chem64/RECU/readme/RECU_1.png

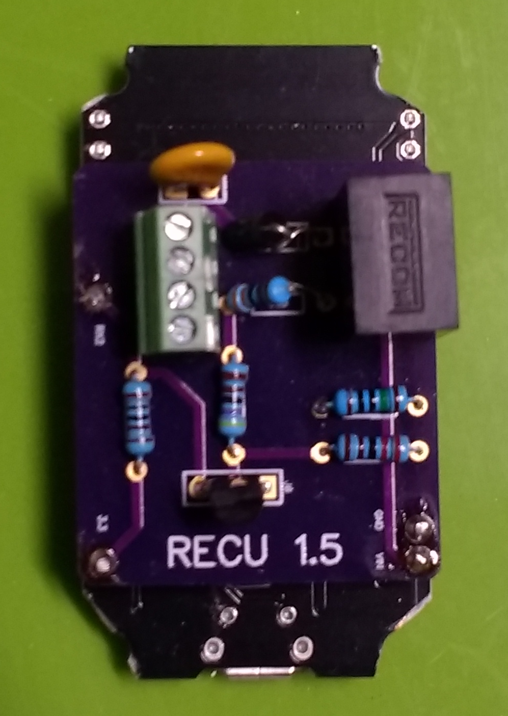
readme/RECU_1.png
