chem64/RECU/readme/Screenshot_after_mat.png

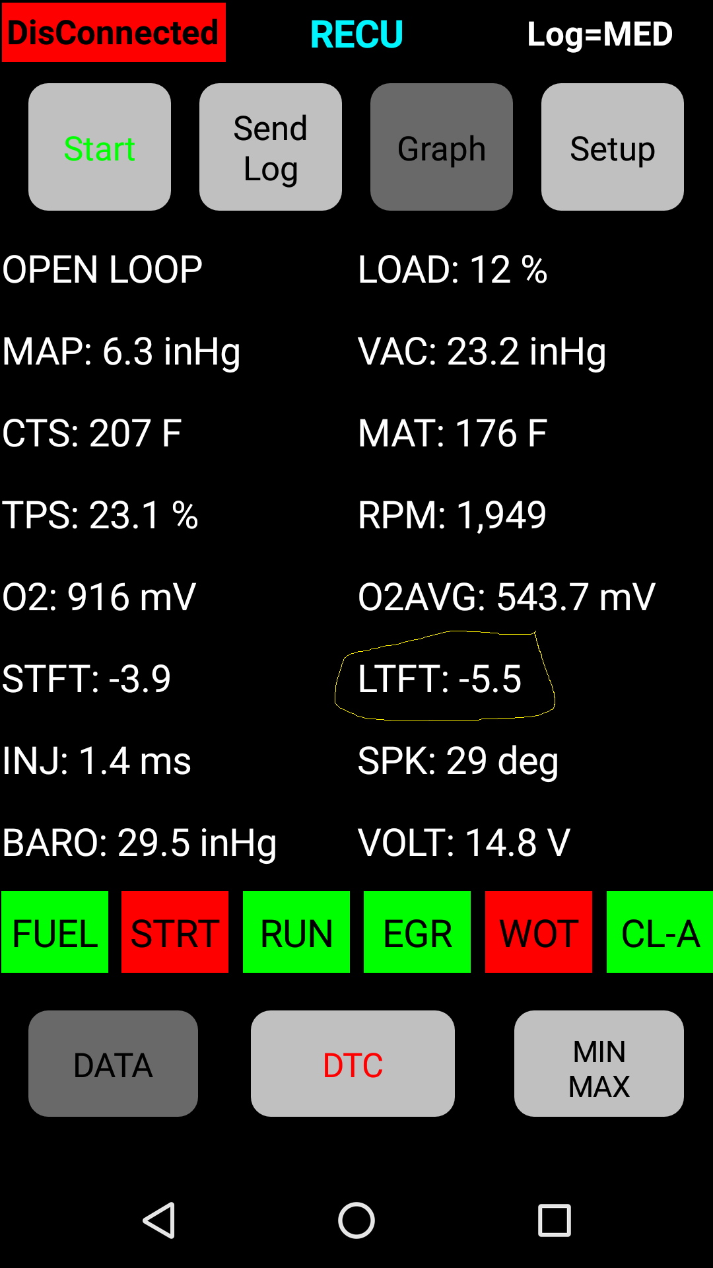
readme/Screenshot_after_mat.png
