chem64/RECU/readme/Screenshot_before_PCV.png

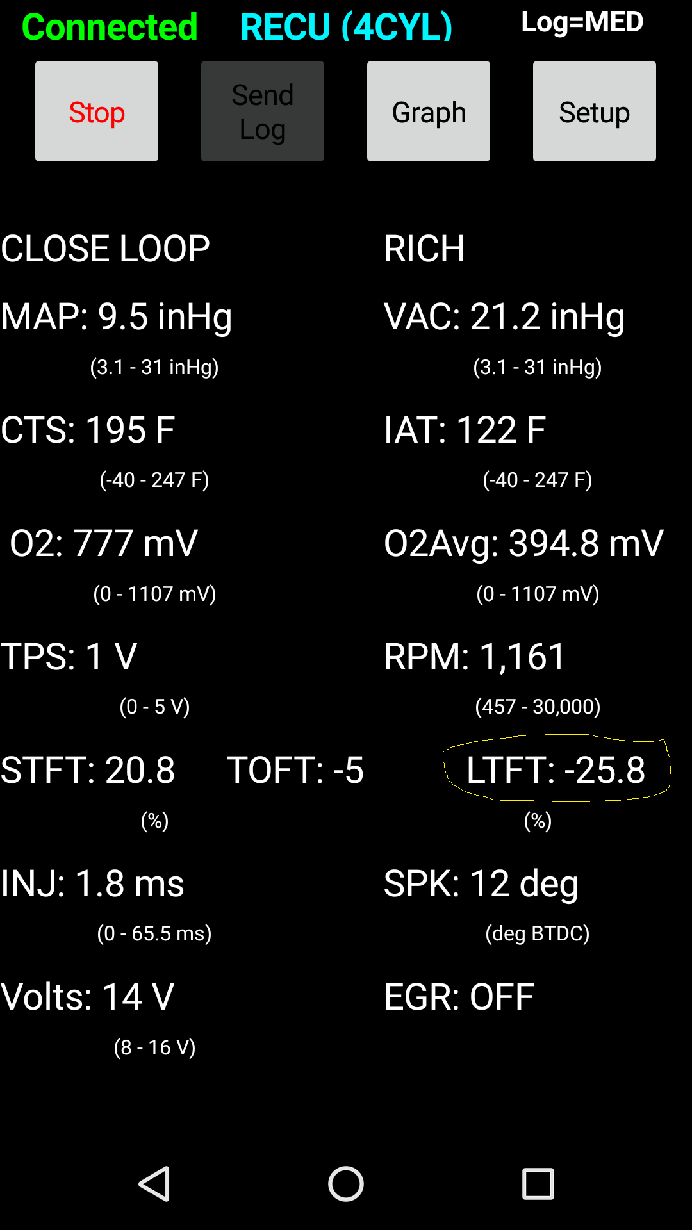
readme/Screenshot_before_PCV.png
